dtatum7/HackRF-UHF-Front-End/Hardware/Amp_1.sch

## KiCad design Hardware/Amp_1.sch (2020-07-21)

Schematic: Amp_1.sch

Parts:
C1, C3, C4, C6: 600S101; R_0603_1608Metric
C2: ATC_600S_4.3p; R_0603_1608Metric
C5: ATC_600S_0.8p; R_0603_1608Metric
L1: 0603HP-15NX; R_0603_1608Metric
L2: 0603HP-R22X; R_0603_1608Metric
L3: 0603HP-8N7X; R_0603_1608Metric
U1: SPF5189Z; SOT-89-3_Qorvo_SPF5189z
