dtatum7/HackRF-UHF-Front-End/Hardware/Amp_2.sch

## KiCad design Hardware/Amp_2.sch (2020-07-21)

Schematic: Amp_2.sch

Parts:
C7, C9, C10, C12: 600S101; R_0603_1608Metric
C8: ATC_600S_4.3p; R_0603_1608Metric
C11: ATC_600S_0.8p; R_0603_1608Metric
L4: 0603HP-15NX; R_0603_1608Metric
L5: 0603HP-R22X; R_0603_1608Metric
L6: 0603HP-8N7X; R_0603_1608Metric
U2: SPF5189Z; SOT-89-3_Qorvo_SPF5189z
