dtatum7/HackRF-UHF-Front-End/Hardware/Chebyshev_Input_BPF_R0.sch

## KiCad design Hardware/Chebyshev_Input_BPF_R0.sch (2020-08-03)

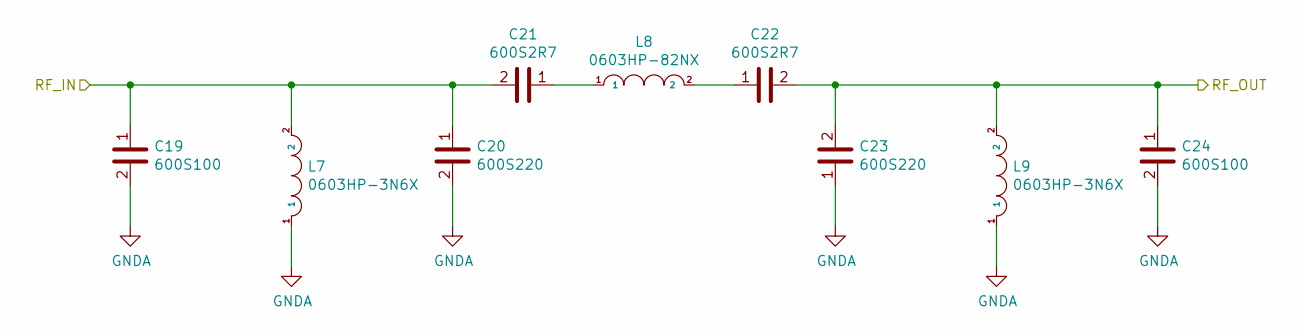
[picture p5: schematic Chebyshev_Input_BPF_R0.sch]

Parts:
C19, C24: 600S100; C_0603_1608Metric
C20, C23: 600S220; C_0603_1608Metric
C21, C22: 600S2R7; C_0603_1608Metric
L7, L9: 0603HP-3N6X; L_0603_1608Metric
L8: 0603HP-82NX; L_0603_1608Metric

Connections:
GNDA: C19.2, C20.2, C23.1, C24.2, L7.1, L9.1
unnamed: C21.1, L8.1
unnamed: C22.1, L8.2
RF_IN: C19.1, C20.1, C21.2, L7.2
RF_OUT: C22.2, C23.2, C24.1, L9.2
