dtatum7/HackRF-UHF-Front-End/Hardware/HACKRF-UHF-RFFE.sch

## KiCad design Hardware/HACKRF-UHF-RFFE.sch (2020-08-03)

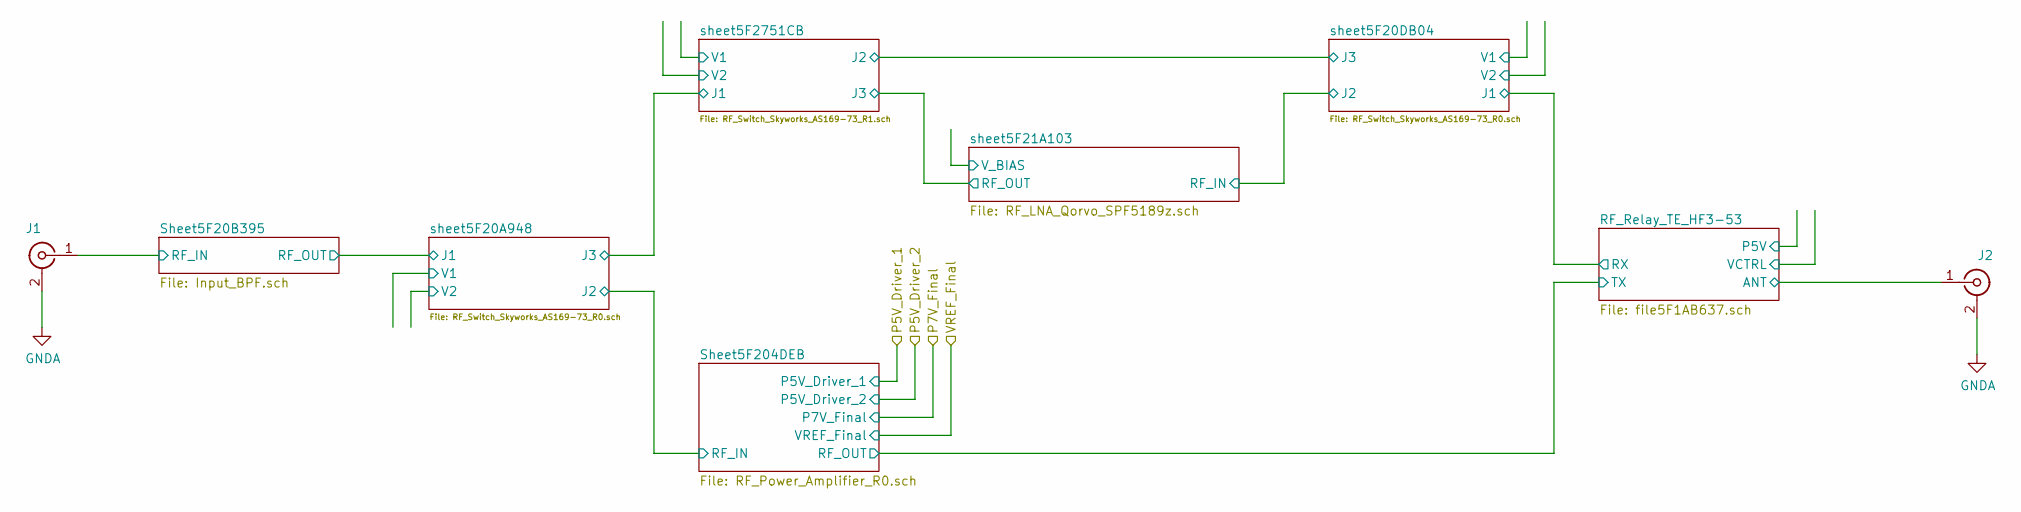
[picture p6: schematic HACKRF-UHF-RFFE.sch]

Parts:
J1, J2: SMA_Wurth_60312242114510

Connections:
ANT: J2.1 (In)
GNDA: J1.2 (Ext), J2.2 (Ext)
RF_IN: J1.1 (In)
