dtatum7/HackRF-UHF-Front-End/Hardware/RF_Attenuator_10dB_0603_R0.sch

## KiCad design Hardware/RF_Attenuator_10dB_0603_R0.sch (2020-08-03)

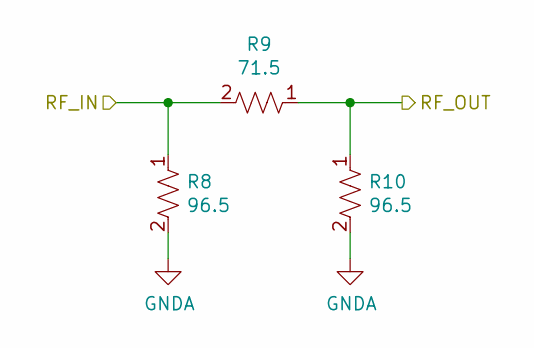
[picture p7: schematic RF_Attenuator_10dB_0603_R0.sch]

Parts:
R8, R10: RT0603DRE0796R5L; R_0603_1608Metric
R9: RT0603BRD0771R5L; R_0603_1608Metric

Connections:
GNDA: R8.2, R10.2
RF_IN: R8.1, R9.2
RF_OUT: R9.1, R10.1
