dtatum7/HackRF-UHF-Front-End/Hardware/RF_Attenuator_0603.sch

## KiCad design Hardware/RF_Attenuator_0603.sch (2020-07-24)

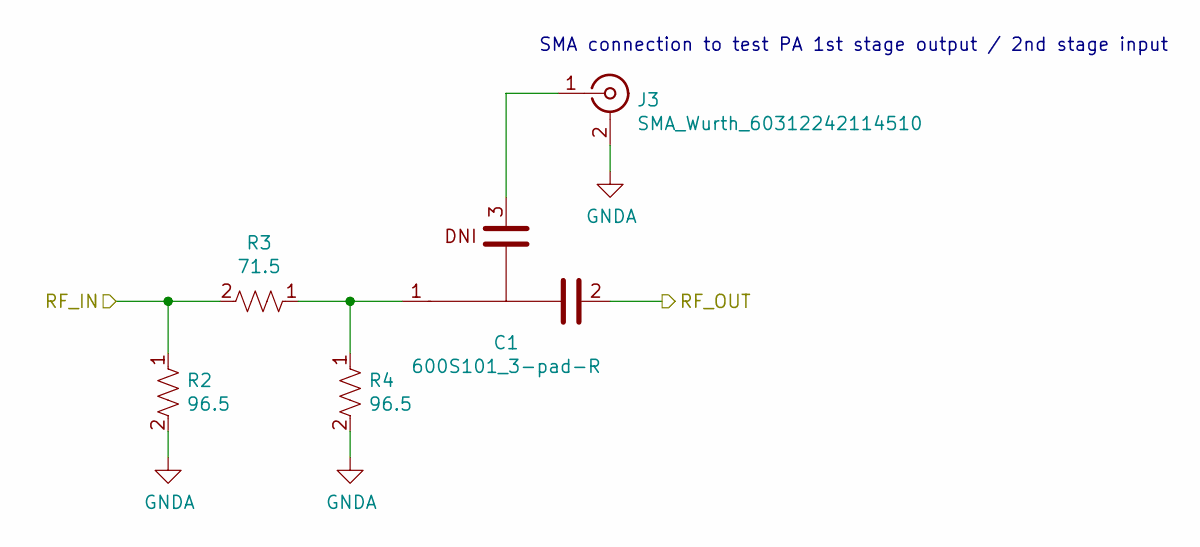
[picture p8: schematic RF_Attenuator_0603.sch]

Parts:
C1: 600S101_3-pad-R; C_0603_1608Metric_3-pad-R
J3: SMA_Wurth_60312242114510
R2, R4: RT0603DRE0796R5L; R_0603_1608Metric
R3: RT0603BRD0771R5L; R_0603_1608Metric

Connections:
GNDA: J3.2 (Ext), R2.2, R4.2
unnamed: C1.1, R3.1, R4.1
unnamed: C1.3, J3.1 (In)
RF_IN: R2.1, R3.2
RF_OUT: C1.2

Notes on the sheet:
SMA connection to test PA 1st stage output / 2nd stage input
