dtatum7/HackRF-UHF-Front-End/Hardware/RF_Attenuator_0603_R0.sch

## KiCad design Hardware/RF_Attenuator_0603_R0.sch (2020-08-03)

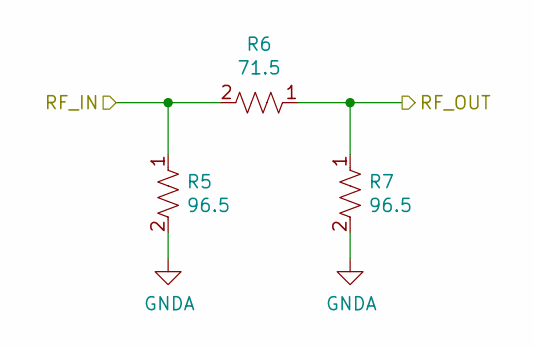
[picture p9: schematic RF_Attenuator_0603_R0.sch]

Parts:
R2, R4: RT0603DRE0796R5L; R_0603_1608Metric
R3: RT0603BRD0771R5L; R_0603_1608Metric

Connections:
GNDA: R2.2, R4.2
RF_IN: R2.1, R3.2
RF_OUT: R3.1, R4.1
