dtatum7/HackRF-UHF-Front-End/Hardware/RF_LNA_Qorvo_SPF5189z.sch

## KiCad design Hardware/RF_LNA_Qorvo_SPF5189z.sch (2020-08-03)

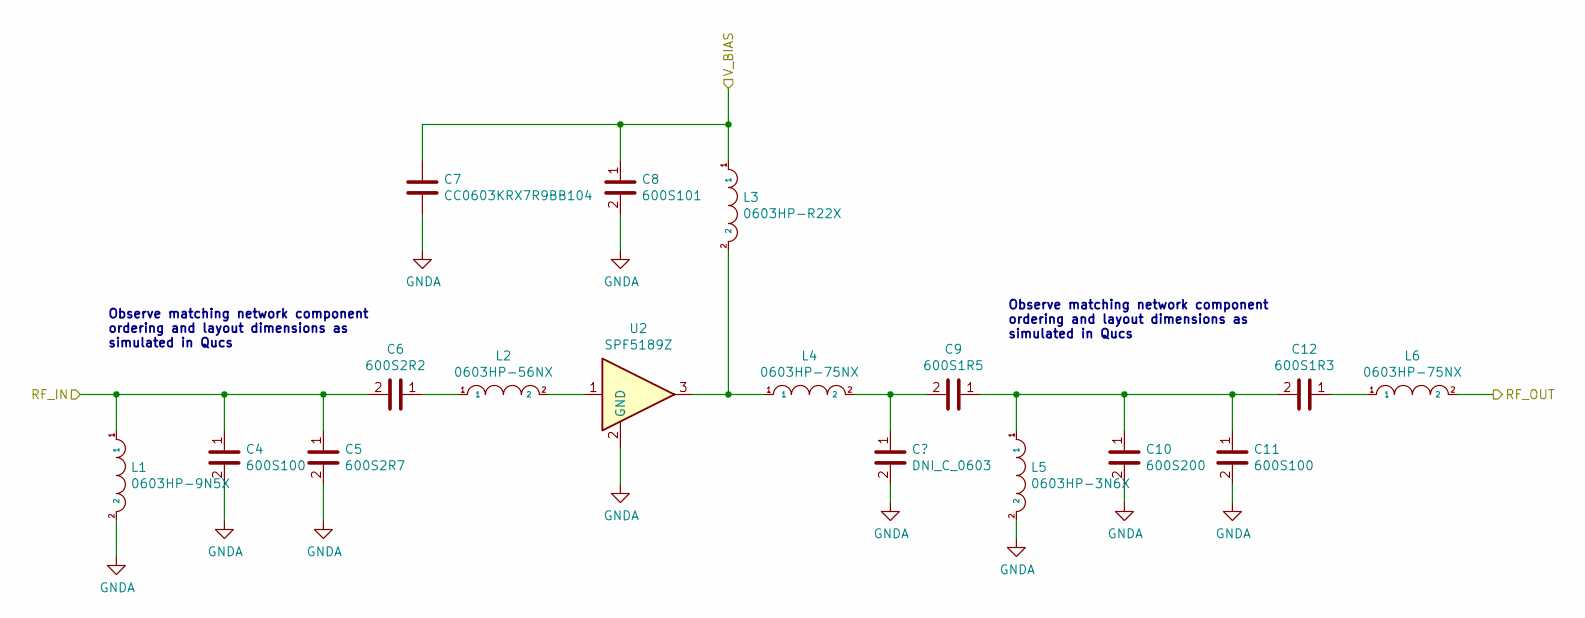
[picture p10: schematic RF_LNA_Qorvo_SPF5189z.sch]

Parts:
C4, C11: 600S100; C_0603_1608Metric
C5: 600S2R7; C_0603_1608Metric
C6: 600S2R2; C_0603_1608Metric
C7: CC0603KRX7R9BB104; C_0603_1608Metric
C8: 600S101; C_0603_1608Metric
C9: 600S1R5; C_0603_1608Metric
C10: 600S200; C_0603_1608Metric
C12: 600S1R3; C_0603_1608Metric
L1: 0603HP-9N5X; L_0603_1608Metric
L2: 0603HP-56NX; L_0603_1608Metric
L3: 0603HP-R22X; R_0603_1608Metric
L4, L6: 0603HP-75NX; L_0603_1608Metric
L5: 0603HP-3N6X; L_0603_1608Metric
U2: SPF5189Z; SOT-89-3_Qorvo_SPF5189z

Connections:
GNDA: C4.2, C5.2, C7.2, C8.2, C10.2, C11.2, L1.2, L5.2, U2.2 (GND)
unnamed: C6.1, L2.1
unnamed: C9.2, L4.2
unnamed: C9.1, C10.1, C11.1, C12.2, L5.1
unnamed: C12.1, L6.1
unnamed: L2.2, U2.1
unnamed: L3.2, L4.1, U2.3
RF_IN: C4.1, C5.1, C6.2, L1.1
RF_OUT: L6.2
V_BIAS: C7.1, C8.1, L3.1

Notes on the sheet:
Observe matching network component ordering and layout dimensions as simulated in Qucs
