dtatum7/HackRF-UHF-Front-End/Hardware/RF_Switch_Skyworks_AS169-73.sch

## KiCad design Hardware/RF_Switch_Skyworks_AS169-73.sch (2020-07-21)

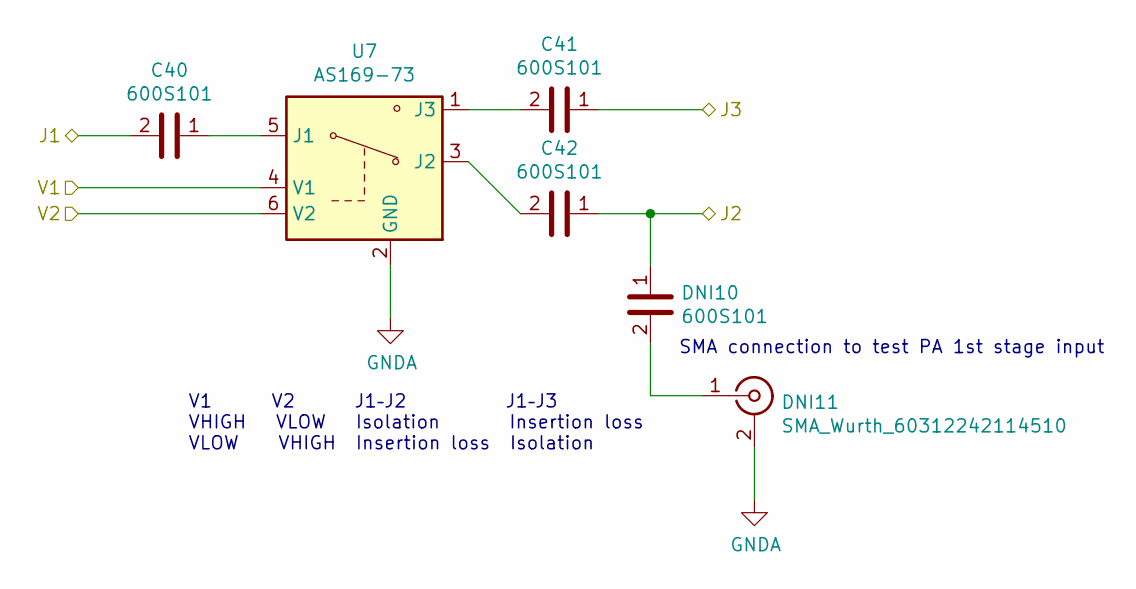
[picture p11: schematic RF_Switch_Skyworks_AS169-73.sch]

Parts:
C28, C29, C30: 600S101; C_0603_1608Metric
DNI6: 600S101; C_0603_1608Metric
DNI9: SMA_Wurth_60312242114510
U4: AS169-73; SOT-23-6

Connections:
GNDA: DNI9.2 (Ext), U4.2 (GND)
J1: C28.2
J2: C30.1, DNI6.1
J3: C29.1
unnamed: C28.1, U4.5 (J1)
unnamed: C29.2, U4.1 (J3)
unnamed: C30.2, U4.3 (J2)
unnamed: DNI6.2, DNI9.1 (In)
V1: U4.4 (V1)
V2: U4.6 (V2)

Notes on the sheet:
V1 V2 J1–J2 J1–J3 VHIGH VLOW Isolation Insertion loss VLOW VHIGH Insertion loss Isolation
SMA connection to test PA 1st stage input
