dtatum7/HackRF-UHF-Front-End/Hardware/RF_Switch_Skyworks_AS169-73_R0.sch

## KiCad design Hardware/RF_Switch_Skyworks_AS169-73_R0.sch (2020-08-03)

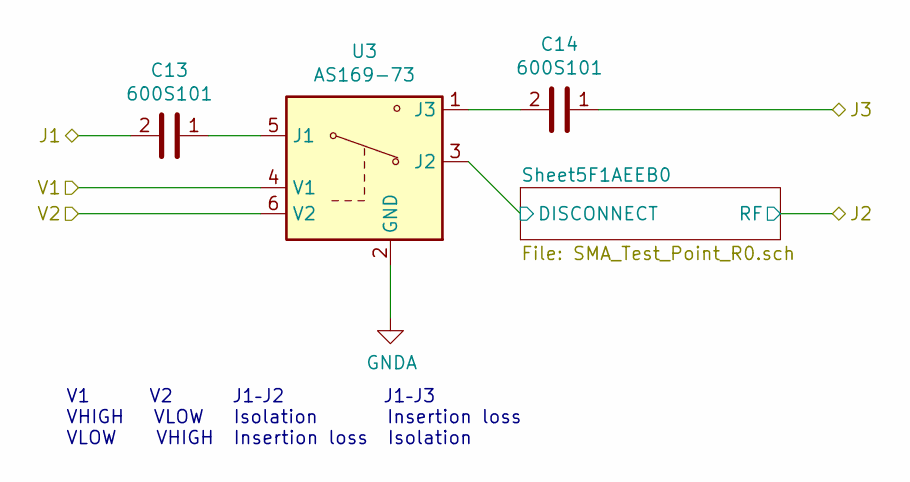
[picture p12: schematic RF_Switch_Skyworks_AS169-73_R0.sch]

Parts:
C1, C2: 600S101; C_0603_1608Metric
U1: AS169-73; SOT-23-6

Connections:
DISCONNECT: U1.3 (J2)
GNDA: U1.2 (GND)
J1: C1.2
J3: C2.1
unnamed: C1.1, U1.5 (J1)
unnamed: C2.2, U1.1 (J3)
V1: U1.4 (V1)
V2: U1.6 (V2)

Notes on the sheet:
V1 V2 J1–J2 J1–J3 VHIGH VLOW Isolation Insertion loss VLOW VHIGH Insertion loss Isolation
