dtatum7/HackRF-UHF-Front-End/Hardware/RF_Switch_Skyworks_AS169-73_R1.sch

## KiCad design Hardware/RF_Switch_Skyworks_AS169-73_R1.sch (2020-08-03)

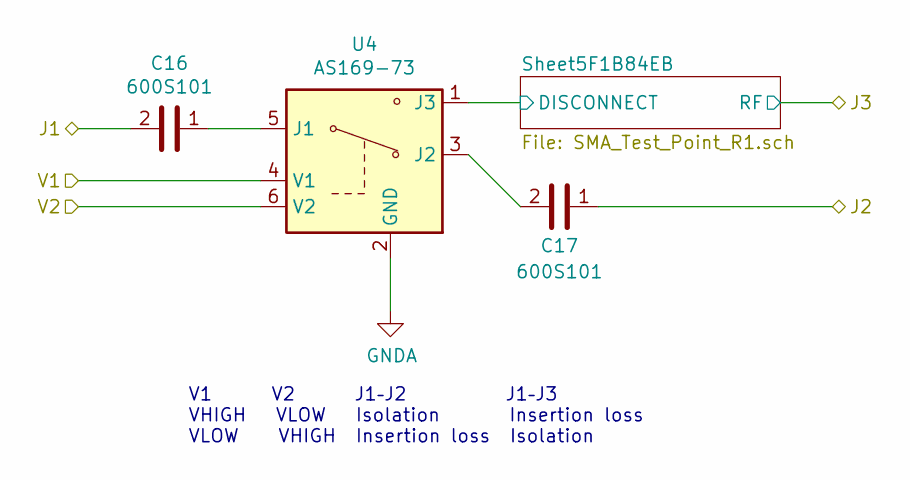
[picture p13: schematic RF_Switch_Skyworks_AS169-73_R1.sch]

Parts:
C16, C17: 600S101; C_0603_1608Metric
U4: AS169-73; SOT-23-6

Connections:
DISCONNECT: U4.1 (J3)
GNDA: U4.2 (GND)
J1: C16.2
J2: C17.1
unnamed: C16.1, U4.5 (J1)
unnamed: C17.2, U4.3 (J2)
V1: U4.4 (V1)
V2: U4.6 (V2)

Notes on the sheet:
V1 V2 J1–J2 J1–J3 VHIGH VLOW Isolation Insertion loss VLOW VHIGH Insertion loss Isolation
