dtatum7/HackRF-UHF-Front-End/Hardware/SMA_Test_Point_R0.sch

## KiCad design Hardware/SMA_Test_Point_R0.sch (2020-08-03)

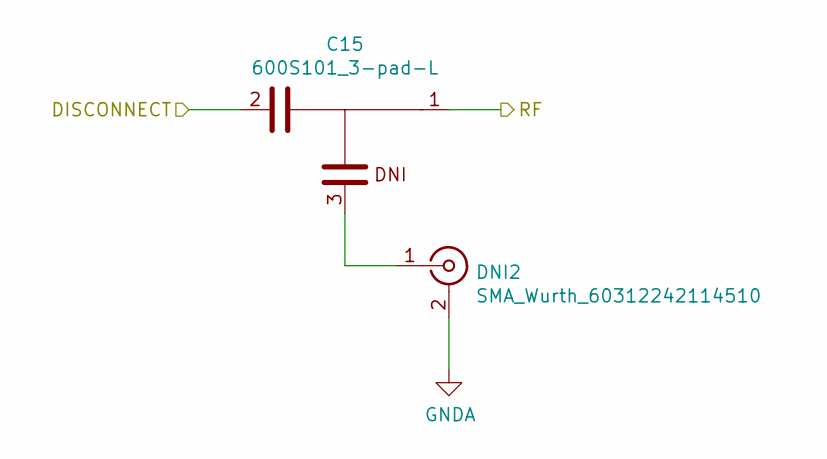
[picture p14: schematic SMA_Test_Point_R0.sch]

Parts:
C3: 600S101_3-pad-L; C_0603_1608Metric_3-pad-L
DNI1: SMA_Wurth_60312242114510

Connections:
DISCONNECT: C3.2
GNDA: DNI1.2 (Ext)
unnamed: C3.3, DNI1.1 (In)
RF: C3.1
