dtatum7/HackRF-UHF-Front-End/Hardware/SMA_Test_Point_R1.sch

## KiCad design Hardware/SMA_Test_Point_R1.sch (2020-08-03)

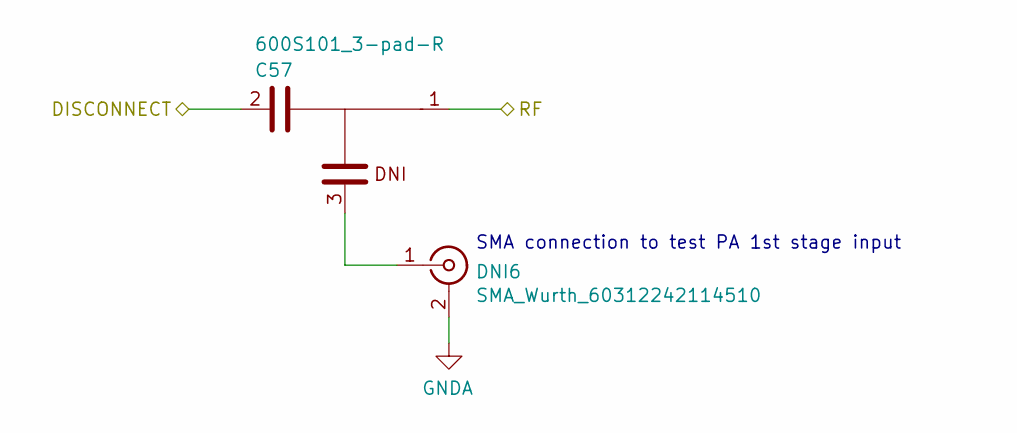
[picture p15: schematic SMA_Test_Point_R1.sch]

Parts:
C18: 600S101_3-pad-R; C_0603_1608Metric_3-pad-R
DNI3: SMA_Wurth_60312242114510

Connections:
DISCONNECT: C18.2
GNDA: DNI3.2 (Ext)
unnamed: C18.3, DNI3.1 (In)
RF: C18.1

Notes on the sheet:
SMA connection to test PA 1st stage input
