dtatum7/HackRF-UHF-Front-End/Hardware/file5F1AB637.sch

## KiCad design Hardware/file5F1AB637.sch (2020-08-03)

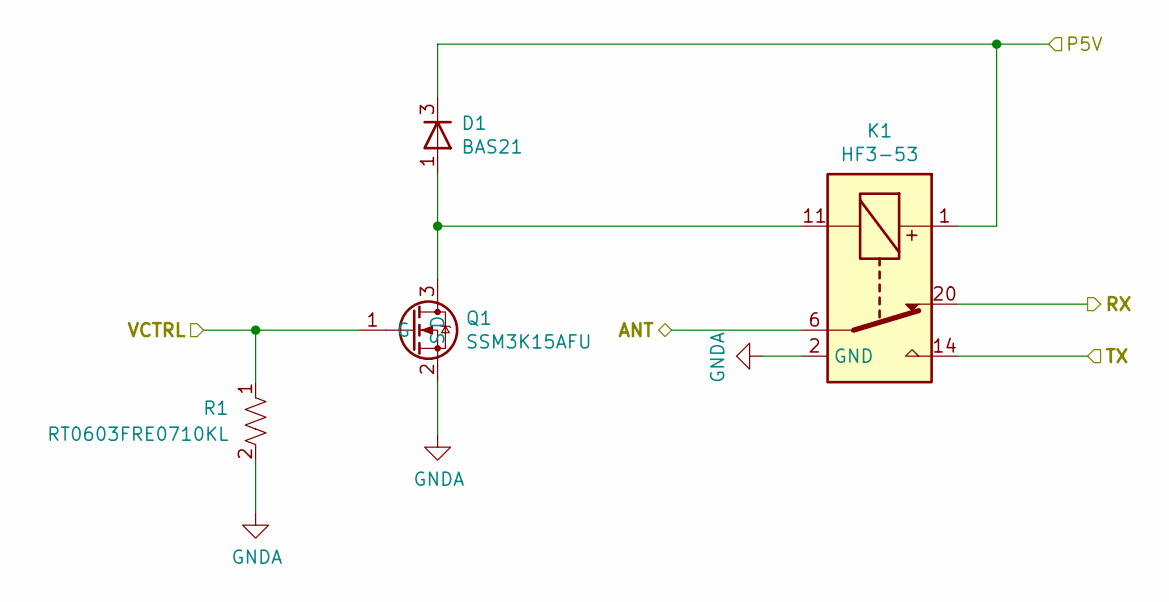
[picture p16: schematic file5F1AB637.sch]

Parts:
D1: BAS21; SOT-23
K1: HF3-53; Relay_SPDT_AXICOM_HF3Series_50ohms_Pitch1.27mm
Q1: SSM3K15AFU; SOT-323_SC-70
R1: RT0603FRE0710KL; R_0603_1608Metric

Connections:
ANT: K1.6
GNDA: K1.2 (GND), K1.5 (GND), K1.7 (GND), K1.10 (GND), K1.12 (GND), K1.13 (GND), K1.15 (GND), K1.17 (GND), K1.19 (GND), K1.21 (GND), K1.22 (GND), Q1.2 (S), R1.2
unnamed: D1.1, K1.11, Q1.3 (D)
P5V: D1.3, K1.1
RX: K1.20
TX: K1.14
VCTRL: Q1.1 (G), R1.1
