dtatum7/HackRF-UHF-Front-End/Hardware/file5F1AE899.sch

## KiCad design Hardware/file5F1AE899.sch (2020-08-03)

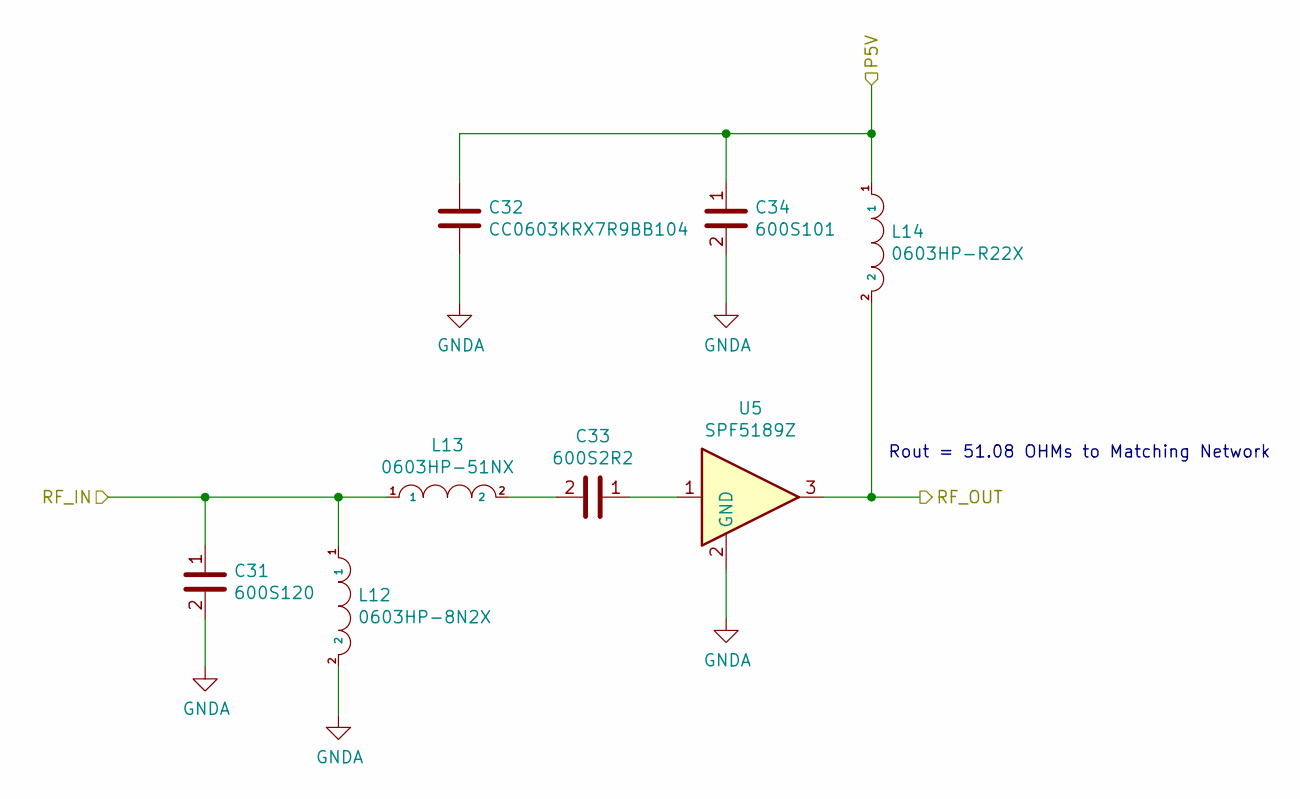
[picture p17: schematic file5F1AE899.sch]

Parts:
C31: 600S120; R_0603_1608Metric
C32: CC0603KRX7R9BB104; C_0603_1608Metric
C33: 600S2R2; R_0603_1608Metric
C34: 600S101; R_0603_1608Metric
L12: 0603HP-8N2X; R_0603_1608Metric
L13: 0603HP-51NX; R_0603_1608Metric
L14: 0603HP-R22X; R_0603_1608Metric
U5: SPF5189Z; SOT-89-3_Qorvo_SPF5189z

Connections:
GNDA: C31.2, C32.2, C34.2, L12.2, U5.2 (GND)
unnamed: C33.1, U5.1
unnamed: C33.2, L13.2
P5V: C32.1, C34.1, L14.1
RF_IN: C31.1, L12.1, L13.1
RF_OUT: L14.2, U5.3

Notes on the sheet:
Rout = 51.08 OHMs to Matching Network
