dtatum7/HackRF-UHF-Front-End/Hardware/file5F1AED06.sch

## KiCad design Hardware/file5F1AED06.sch (2020-08-03)

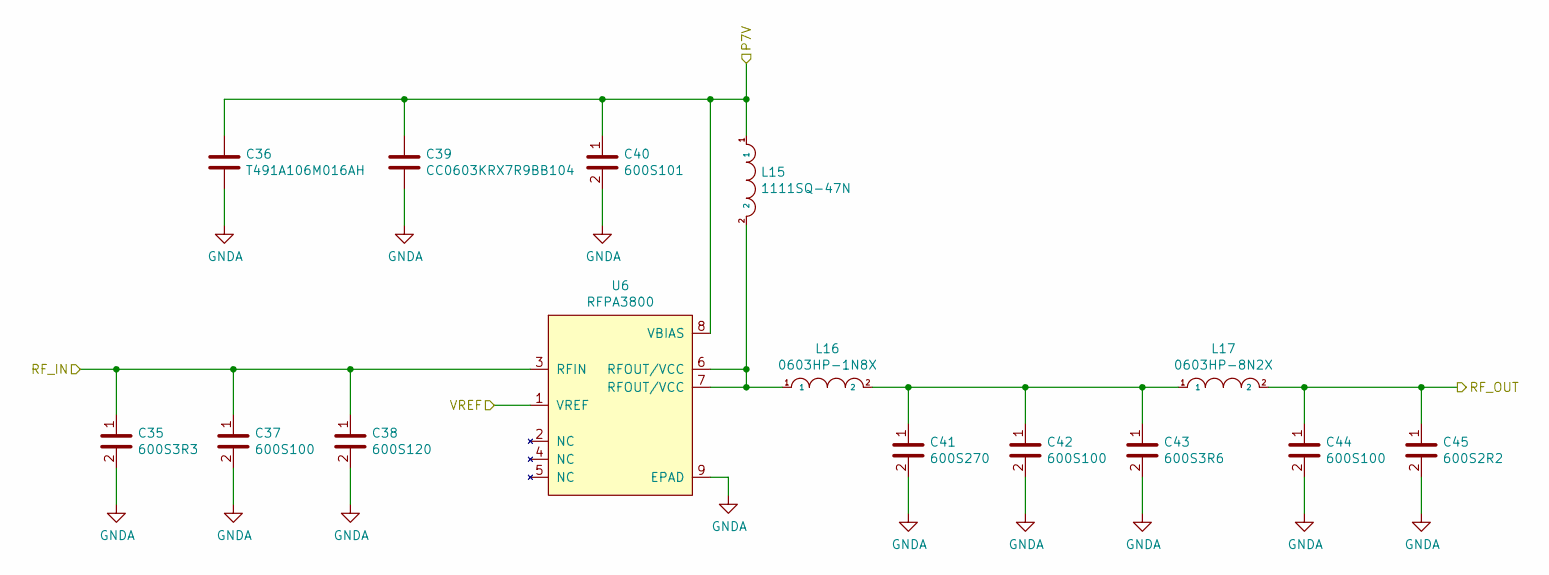
[picture p18: schematic file5F1AED06.sch]

Parts:
C35: 600S3R3; C_0603_1608Metric
C36: T491A106M016AH; C_1206_3216Metric
C37, C42, C44: 600S100; C_0603_1608Metric
C38: 600S120; C_0603_1608Metric
C39: CC0603KRX7R9BB104; C_0603_1608Metric
C40: 600S101; R_0603_1608Metric
C41: 600S270; C_0603_1608Metric
C43: 600S3R6; C_0603_1608Metric
C45: 600S2R2; C_0603_1608Metric
L15: 1111SQ-47N; L_Coilcraft_1111SQ-47N
L16: 0603HP-1N8X; L_0603_1608Metric
L17: 0603HP-8N2X; L_0603_1608Metric
U6: RFPA3800; SOIC-8_Qorvo_RFPA3800

Connections:
GNDA: C35.2, C36.2, C37.2, C38.2, C39.2, C40.2, C41.2, C42.2, C43.2, C44.2, C45.2, U6.9 (EPAD)
unnamed: C41.1, C42.1, C43.1, L16.2, L17.1
unnamed: L15.2, L16.1, U6.6 (RFOUT/VCC), U6.7 (RFOUT/VCC)
P7V: C36.1, C39.1, C40.1, L15.1, U6.8 (VBIAS)
RF_IN: C35.1, C37.1, C38.1, U6.3 (RFIN)
RF_OUT: C44.1, C45.1, L17.2
VREF: U6.1 (VREF)
