dtatum7/HackRF-UHF-Front-End/Hardware/file5F138C05.sch

## KiCad design Hardware/file5F138C05.sch (2020-08-03)

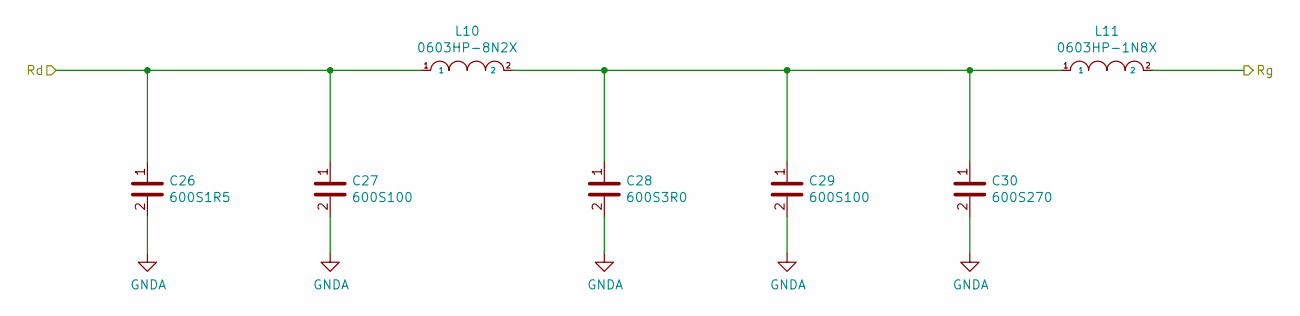
[picture p19: schematic file5F138C05.sch]

Parts:
C26: 600S1R5; C_0603_1608Metric
C27, C29: 600S100; C_0603_1608Metric
C28: 600S3R0; C_0603_1608Metric
C30: 600S270; C_0603_1608Metric
L10: 0603HP-8N2X; L_0603_1608Metric
L11: 0603HP-1N8X; L_0603_1608Metric

Connections:
GNDA: C26.2, C27.2, C28.2, C29.2, C30.2
unnamed: C28.1, C29.1, C30.1, L10.2, L11.1
Rd: C26.1, C27.1, L10.1
Rg: L11.2
